DoctorWkt/MMU09/um6809/6809.c

/*
    6809.c   	-	cycle accurate simple 6809 cpu emulator
    Copyright (C) 2001  Arto Salmi
                        Joze Fabcic

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
    You should have received a copy of the GNU General Public License
    along with this program; if not, write to the Free Software
    Foundation, Inc., 675 Mass Ave, Cambridge, MA 02139, USA.
*/


#include "6809.h"

unsigned X, Y, S, U, PC;
unsigned A, B, DP;
unsigned H, N, Z, V, C;
unsigned EFI;

unsigned iPC;

UINT8 *memory = NULL;

unsigned ea = 0;
int cpu_clk = 0;
int cpu_period = 0;
int cpu_quit = 1;

unsigned *index_regs[4] = { &X, &Y, &U, &S };

unsigned imm_byte (void)
{
  unsigned val = memory[PC & 0xffff]; PC++;
  return val;
}

unsigned imm_word (void)
{
  unsigned val = (memory[PC & 0xffff] << 8) | memory[(PC + 1) & 0xffff]; PC += 2; 
  return val;
}

static void WRMEM (unsigned addr, unsigned data)
{
  memory[addr] = (UINT8)data;
}

void WRMEM16 (unsigned addr, unsigned data)
{
  WRMEM(addr,data >> 8);
  cpu_clk--;
  WRMEM((addr + 1) & 0xffff,data & 0xff);
}

unsigned RDMEM (unsigned addr)
{
  return memory[addr];
}

unsigned RDMEM16 (unsigned addr)
{
  unsigned val = RDMEM(addr) << 8;
  cpu_clk--;
  val |= RDMEM((addr + 1) & 0xffff);
  return val;
}

#define write_stack WRMEM
#define read_stack  RDMEM

void write_stack16 (unsigned addr, unsigned data)
{
  write_stack((addr + 1) & 0xffff,data & 0xff); 
  write_stack(addr,data >> 8);
}

unsigned read_stack16 (unsigned addr)
{
  return (read_stack(addr) << 8) | read_stack((addr + 1) & 0xffff);
}

void direct (void)
{
  unsigned val = memory[PC & 0xffff] | DP; PC++;
  ea = val;
}

void indexed (void) /* note take 1 extra cycle */
{
   unsigned post = imm_byte();
   unsigned *R   = index_regs[(post >> 5) & 0x3];
 
   if (post & 0x80)
   {
     switch (post & 0x1f)
     {
       case 0x00: ea = *R; *R = (*R + 1) & 0xffff;                  cpu_clk -= 6; break;
       case 0x01: ea = *R; *R = (*R + 2) & 0xffff;                  cpu_clk -= 7; break;
       case 0x02: *R = (*R - 1) & 0xffff; ea = *R;                  cpu_clk -= 6; break;
       case 0x03: *R = (*R - 2) & 0xffff; ea = *R;                  cpu_clk -= 7; break;
       case 0x04: ea = *R;                                          cpu_clk -= 4; break;
       case 0x05: ea = (*R + ((INT8)B)) & 0xffff;                   cpu_clk -= 5; break;
       case 0x06: ea = (*R + ((INT8)A)) & 0xffff;                   cpu_clk -= 5; break;
       case 0x08: ea = (*R + ((INT8)imm_byte())) & 0xffff;          cpu_clk -= 5; break;
       case 0x09: ea = (*R + imm_word()) & 0xffff;                  cpu_clk -= 8; break;
       case 0x0b: ea = (*R + get_d()) & 0xffff;                     cpu_clk -= 8; break;
       case 0x0c: ea = (INT8)imm_byte(); ea = (ea + PC) & 0xffff;   cpu_clk -= 5; break; 
       case 0x0d: ea = imm_word(); ea = (ea + PC) & 0xffff;         cpu_clk -= 9; break;

       case 0x11: ea = *R; *R = (*R + 2) & 0xffff;                  cpu_clk -= 7; ea = RDMEM16(ea); cpu_clk -= 2; break;
       case 0x13: *R = (*R - 2) & 0xffff; ea = *R;                  cpu_clk -= 7; ea = RDMEM16(ea); cpu_clk -= 2; break;
       case 0x14: ea = *R;                                          cpu_clk -= 4; ea = RDMEM16(ea); cpu_clk -= 2; break;
       case 0x15: ea = (*R + ((INT8)B)) & 0xffff;                   cpu_clk -= 5; ea = RDMEM16(ea); cpu_clk -= 2; break;
       case 0x16: ea = (*R + ((INT8)A)) & 0xffff;                   cpu_clk -= 5; ea = RDMEM16(ea); cpu_clk -= 2; break;
       case 0x18: ea = (*R + ((INT8)imm_byte())) & 0xffff;          cpu_clk -= 5; ea = RDMEM16(ea); cpu_clk -= 2; break;
       case 0x19: ea = (*R + imm_word()) & 0xffff;                  cpu_clk -= 8; ea = RDMEM16(ea); cpu_clk -= 2; break;
       case 0x1b: ea = (*R + get_d()) & 0xffff;                     cpu_clk -= 8; ea = RDMEM16(ea); cpu_clk -= 2; break;
       case 0x1c: ea = (INT8)imm_byte(); ea = (ea + PC) & 0xffff;   cpu_clk -= 5; ea = RDMEM16(ea); cpu_clk -= 2; break;
       case 0x1d: ea = imm_word(); ea = (ea + PC) & 0xffff;         cpu_clk -= 9; ea = RDMEM16(ea); cpu_clk -= 2; break;
       case 0x1f: ea = imm_word();                                  cpu_clk -= 6; ea = RDMEM16(ea); cpu_clk -= 2; break;      
       default:   ea = 0;  printf("%X: invalid index post $%02X\n",iPC,post); monitor_on = 1;                     break;
     }
   }
   else
   {
     if( post & 0x10) post |= 0xfff0; else post &= 0x000f;
     ea = (*R + post) & 0xffff;
     cpu_clk -= 5;
   }
}

void extended (void)
{
  unsigned val = (memory[PC & 0xffff] << 8) | memory[(PC + 1) & 0xffff]; PC += 2; 
  ea = val;
}

/* external register functions */

unsigned get_a  (void) { return A; }
unsigned get_b  (void) { return B; } 
unsigned get_dp (void) { return DP >> 8; }
unsigned get_x  (void) { return X; }
unsigned get_y  (void) { return Y; }
unsigned get_s  (void) { return S; }
unsigned get_u  (void) { return U; }
unsigned get_pc (void) { return PC & 0xffff; }
unsigned get_d  (void) { return (A<<8)|B; }

void set_a  (unsigned val) { A = val & 0xff; }
void set_b  (unsigned val) { B = val & 0xff; }
void set_dp (unsigned val) { DP = (val & 0xff) << 8; }
void set_x  (unsigned val) { X = val & 0xffff; }
void set_y  (unsigned val) { Y = val & 0xffff; }
void set_s  (unsigned val) { S = val & 0xffff; }
void set_u  (unsigned val) { U = val & 0xffff; }
void set_pc (unsigned val) { PC = val & 0xffff; }
void set_d  (unsigned val) { A = (val >> 8) & 0xff; B = val & 0xff; }

/* handle condition code register */

unsigned get_cc (void)
{
  unsigned res = EFI & (E_FLAG|F_FLAG|I_FLAG);

  if(H & 0x10) res |= H_FLAG;
  if(N & 0x80) res |= N_FLAG;
  if(Z == 0)   res |= Z_FLAG;
  if(V & 0x80) res |= V_FLAG;
  if(C != 0)   res |= C_FLAG;

  return res;
}

void set_cc (unsigned arg)
{
  EFI =   arg & (E_FLAG|F_FLAG|I_FLAG);
  H   =  (arg & H_FLAG ? 0x10 : 0);
  N   =  (arg & N_FLAG ? 0x80 : 0);
  Z   = (~arg)& Z_FLAG;
  V   =  (arg & V_FLAG ? 0x80 : 0);
  C   =   arg & C_FLAG; 
}

unsigned get_reg (unsigned nro)
{
  unsigned val = 0xff;

  switch (nro)
  {
    case  0: val = (A << 8) | B; break;
    case  1: val = X;            break;
    case  2: val = Y;            break;
    case  3: val = U;            break;
    case  4: val = S;            break;
    case  5: val = PC & 0xffff;  break;
    case  8: val = A;            break;
    case  9: val = B;            break;
    case 10: val = get_cc();     break;
    case 11: val = DP >> 8;      break;
  }

  return val;
}

void set_reg (unsigned nro, unsigned val)
{
  switch (nro)
  {
    case  0: A = val >> 8;
             B = val & 0xff; break;
    case  1: X = val;        break;
    case  2: Y = val;        break;
    case  3: U = val;        break;
    case  4: S = val;        break;
    case  5: PC = val;       break;
    case  8: A = val;        break;
    case  9: B = val;        break;
    case 10: set_cc(val);    break;
    case 11: DP = val << 8;  break;
  }
}

/* 8-Bit Accumulator and Memory Instructions */

unsigned adc (unsigned arg, unsigned val)
{
  unsigned res = arg + val + (C != 0);

  C = (res >> 1) & 0x80;
  N = Z = res &= 0xff;
  V = H = arg ^ val ^ res ^ C;
  
  return res;
}

unsigned add (unsigned arg, unsigned val)
{
  unsigned res = arg + val;

  C = (res >> 1) & 0x80;
  N = Z = res &= 0xff;
  V = H = arg ^ val ^ res ^ C;
 
  return res;
}

unsigned and (unsigned arg, unsigned val)
{
  unsigned res = arg & val;

  N = Z = res;
  V = 0;

  return res;
}

unsigned asl (unsigned arg) /* same as lsl */
{
  unsigned res = arg << 1;

  C = res & 0x100;
  N = Z = res &= 0xff;
  V = arg ^ res;
  cpu_clk -= 2;

  return res;
}

unsigned asr (unsigned arg)
{
  unsigned res = (INT8)arg;

  C = res & 1;
  N = Z = res = (res >> 1) & 0xff;
  cpu_clk -= 2;

  return res;
}

void bit (unsigned arg, unsigned val)
{
  unsigned res = arg & val;

  N = Z = res;
  V = 0;
}

unsigned clr (unsigned arg)
{
  C = N = Z = V = arg = 0;
  cpu_clk -= 2;

  return arg;
}

void cmp (unsigned arg, unsigned val)
{
  unsigned res = arg - val;

  C = res & 0x100;
  N = Z = res &= 0xff;
  V = (arg ^ val) & (arg ^ res);
}

unsigned com (unsigned arg)
{
  unsigned res = arg ^ 0xff;

  N = Z = res;
  V = 0; C = 1;
  cpu_clk -= 2;

  return res;
}

void daa (void)
{
  unsigned res = A;
  unsigned msn = res & 0xf0;
  unsigned lsn = res & 0x0f;

  if( lsn>0x09 || (H & 0x10)) res += 0x06;
  if( msn>0x80 &&   lsn>0x09) res += 0x60;
  if( msn>0x90 ||   (C != 0)) res += 0x60;

  C |= (res & 0x100);
  A = N = Z = res &= 0xff;
  V = 0; /* fix this */

  cpu_clk -= 2;
}

unsigned dec (unsigned arg)
{
  unsigned res = (arg - 1) & 0xff;

  N = Z = res;
  V = arg & ~res;
  cpu_clk -= 2;

  return res;
}

unsigned eor (unsigned arg, unsigned val)
{
  unsigned res = arg ^ val;

  N = Z = res;
  V = 0;

  return res;
}

void exg (void)
{
  unsigned tmp1 = 0xff;
  unsigned tmp2 = 0xff;
  unsigned post = imm_byte();

  if(((post ^ (post << 4)) & 0x80) == 0)
  {
    tmp1 = get_reg(post >> 4);
    tmp2 = get_reg(post & 15);
  }

  set_reg(post & 15, tmp1);
  set_reg(post >> 4, tmp2);

  cpu_clk -= 8;
}

unsigned inc (unsigned arg)
{
  unsigned res = (arg + 1) & 0xff;

  N = Z = res;
  V = ~arg & res;
  cpu_clk -= 2;

  return res;
}

unsigned ld (unsigned arg)
{
  unsigned res = arg;

  N = Z = res;
  V = 0;

  return res;
}

unsigned lsr (unsigned arg)
{
  unsigned res = arg >> 1;
 
  N = 0;
  Z = res;
  C = arg & 1;
  cpu_clk -= 2;

  return res;
}

void mul (void)
{
  unsigned res = (A * B) & 0xffff;

  Z = res;
  C = res & 0x80;
  A = res >> 8;
  B = res & 0xff;
  cpu_clk -= 11; 
}

unsigned neg (int arg)
{
  unsigned res = (-arg) & 0xff;

  C = N = Z = res;
  V = res & arg;
  cpu_clk -= 2;

  return res;
}

unsigned or (unsigned arg, unsigned val)
{
  unsigned res = arg | val;

  N = Z = res;
  V = 0;

  return res;
}

unsigned rol (unsigned arg)
{
  unsigned res = (arg << 1) + (C != 0);

  C = res & 0x100;
  N = Z = res &= 0xff;
  V = arg ^ res;
  cpu_clk -= 2;

  return res;
}

unsigned ror (unsigned arg)
{
  unsigned res = arg;

  if(C != 0) res |= 0x100;
  C = res & 1;
  N = Z = res >>= 1;
  cpu_clk -= 2;

  return res;
}

unsigned sbc (unsigned arg, unsigned val)
{
  unsigned res = arg - val - (C != 0);

  C = res & 0x100;
  N = Z = res &= 0xff;
  V = (arg ^ val) & (arg ^ res);

  return res;
}

void st (unsigned arg)
{
  unsigned res = arg;

  N = Z = res;
  V = 0;
  
  WRMEM(ea,res);
}

unsigned sub (unsigned arg, unsigned val)
{
  unsigned res = arg - val;

  C = res & 0x100;
  N = Z = res &= 0xff;
  V = (arg ^ val) & (arg ^ res);

  return res;
}

void tst (unsigned arg)
{
  unsigned res = arg;

  N = Z = res;
  V = 0;
  cpu_clk -= 2;
}

void tfr (void)
{
  unsigned tmp1 = 0xff;
  unsigned post = imm_byte();

  if(((post ^ (post << 4)) & 0x80) == 0) tmp1 = get_reg(post >> 4);

  set_reg(post & 15, tmp1);

  cpu_clk -= 6;
}


/* 16-Bit Accumulator Instructions */

void abx (void)
{
  X = (X + B) & 0xffff;
  cpu_clk -= 3;
}

void addd (unsigned val)
{
  unsigned arg = (A << 8) | B;
  unsigned res = arg + val;

  C = res & 0x10000;
  Z = res &= 0xffff;
  V = ((arg^res) & (val^res)) >> 8;
  A = N = res >> 8;
  B = res & 0xff;
}

void cmp16 (unsigned arg, unsigned val)
{
  unsigned res = arg - val;

  C = res & 0x10000;
  Z = res &= 0xffff;
  N = res >> 8;
  V = ((arg ^ val) & (arg ^ res)) >> 8;
}

void ldd (unsigned arg)
{
  unsigned res = arg;

  Z = res;
  A = N = res >> 8;
  B = res & 0xff;
  V = 0;
}

unsigned ld16 (unsigned arg)
{
  unsigned res = arg;

  Z = res;
  N = res >> 8;
  V = 0;

  return res;
}

void sex (void)
{
  unsigned res = B;

  Z = res;
  N = res &= 0x80;
  if(res != 0) res = 0xff;
  A = res;
  cpu_clk -= 2;
}

void std (void)
{
  unsigned res = (A << 8) | B;

  Z = res;
  N = A;
  V = 0;
  WRMEM16(ea,res);
}

void st16 (unsigned arg)
{
  unsigned res = arg;

  Z = res;
  N = res >> 8;
  V = 0;
  WRMEM16(ea,res);
}

void subd (unsigned val)
{
  unsigned arg = (A << 8) | B;
  unsigned res = arg - val;

  C = res & 0x10000;
  Z = res &= 0xffff;
  V = ((arg ^ val) & (arg ^ res)) >> 8;
  A = N = res >> 8;
  B = res & 0xff;
}

/* stack instructions */

void pshs (void)
{
  unsigned post = imm_byte();

  cpu_clk -= 5;
  
  if(post & 0x80) { cpu_clk -= 2; S = (S - 2) & 0xffff; write_stack16(S, PC & 0xffff); }
  if(post & 0x40) { cpu_clk -= 2; S = (S - 2) & 0xffff; write_stack16(S, U);      }
  if(post & 0x20) { cpu_clk -= 2; S = (S - 2) & 0xffff; write_stack16(S,  Y);     }
  if(post & 0x10) { cpu_clk -= 2; S = (S - 2) & 0xffff; write_stack16(S,  X);     }
  if(post & 0x08) { cpu_clk -= 1; S = (S - 1) & 0xffff; write_stack(S, DP >> 8);  }
  if(post & 0x04) { cpu_clk -= 1; S = (S - 1) & 0xffff; write_stack(S, B);        }
  if(post & 0x02) { cpu_clk -= 1; S = (S - 1) & 0xffff; write_stack(S, A);        }
  if(post & 0x01) { cpu_clk -= 1; S = (S - 1) & 0xffff; write_stack(S, get_cc()); } 
}

void pshu (void)
{
  unsigned post = imm_byte();

  cpu_clk -= 5;

  if(post & 0x80) { cpu_clk -= 2; U = (U - 2) & 0xffff; write_stack16(U, PC & 0xffff); }
  if(post & 0x40) { cpu_clk -= 2; U = (U - 2) & 0xffff; write_stack16(U, S);      }
  if(post & 0x20) { cpu_clk -= 2; U = (U - 2) & 0xffff; write_stack16(U,  Y);     }
  if(post & 0x10) { cpu_clk -= 2; U = (U - 2) & 0xffff; write_stack16(U,  X);     }
  if(post & 0x08) { cpu_clk -= 1; U = (U - 1) & 0xffff; write_stack(U, DP >> 8);  }
  if(post & 0x04) { cpu_clk -= 1; U = (U - 1) & 0xffff; write_stack(U, B);        }
  if(post & 0x02) { cpu_clk -= 1; U = (U - 1) & 0xffff; write_stack(U, A);        }
  if(post & 0x01) { cpu_clk -= 1; U = (U - 1) & 0xffff; write_stack(U, get_cc()); } 
}

void puls (void)
{
  unsigned post = imm_byte();

  cpu_clk -= 5;

  if(post & 0x01) { cpu_clk -= 1; set_cc(read_stack(S));     S = (S + 1) & 0xffff; }
  if(post & 0x02) { cpu_clk -= 1; A   = read_stack(S);       S = (S + 1) & 0xffff; }
  if(post & 0x04) { cpu_clk -= 1; B   = read_stack(S);       S = (S + 1) & 0xffff; }
  if(post & 0x08) { cpu_clk -= 1; DP  = read_stack(S) << 8;  S = (S + 1) & 0xffff; }
  if(post & 0x10) { cpu_clk -= 2; X   = read_stack16(S);     S = (S + 2) & 0xffff; }
  if(post & 0x20) { cpu_clk -= 2; Y   = read_stack16(S);     S = (S + 2) & 0xffff; }
  if(post & 0x40) { cpu_clk -= 2; U   = read_stack16(S);     S = (S + 2) & 0xffff; }
  if(post & 0x80) { cpu_clk -= 2; PC  = read_stack16(S);     S = (S + 2) & 0xffff; }
}

void pulu (void)
{
  unsigned post = imm_byte();

  cpu_clk -= 5;

  if(post & 0x01) { cpu_clk -= 1; set_cc(read_stack(U));     U = (U + 1) & 0xffff; }
  if(post & 0x02) { cpu_clk -= 1; A   = read_stack(U);       U = (U + 1) & 0xffff; }
  if(post & 0x04) { cpu_clk -= 1; B   = read_stack(U);       U = (U + 1) & 0xffff; }
  if(post & 0x08) { cpu_clk -= 1; DP  = read_stack(U) << 8;  U = (U + 1) & 0xffff; }
  if(post & 0x10) { cpu_clk -= 2; X   = read_stack16(U);     U = (U + 2) & 0xffff; }
  if(post & 0x20) { cpu_clk -= 2; Y   = read_stack16(U);     U = (U + 2) & 0xffff; }
  if(post & 0x40) { cpu_clk -= 2; S   = read_stack16(U);     U = (U + 2) & 0xffff; }
  if(post & 0x80) { cpu_clk -= 2; PC  = read_stack16(U);     U = (U + 2) & 0xffff; }
}

/* Miscellaneous Instructions */

void nop (void)
{
  cpu_clk -= 2;
}

void jsr (void)
{
  S = (S - 2) & 0xffff; write_stack16(S, PC & 0xffff);     
  PC = ea;
}

void rti (void)
{
  cpu_clk -= 6;
  set_cc(read_stack(S));  S = (S + 1) & 0xffff;

  if((EFI & E_FLAG) != 0)
  {
    cpu_clk -= 9;
    A   = read_stack(S);       S = (S + 1) & 0xffff;
    B   = read_stack(S);       S = (S + 1) & 0xffff;
    DP  = read_stack(S) << 8;  S = (S + 1) & 0xffff;
    X   = read_stack16(S);     S = (S + 2) & 0xffff;
    Y   = read_stack16(S);     S = (S + 2) & 0xffff;
    U   = read_stack16(S);     S = (S + 2) & 0xffff;
  }
  PC  = read_stack16(S);     S = (S + 2) & 0xffff;
}

void rts (void)
{
  cpu_clk -= 5;
  PC  = read_stack16(S);     S = (S + 2) & 0xffff;
}

void swi (void)
{
  cpu_clk -= 19;
  EFI |= E_FLAG;
  S = (S - 2) & 0xffff; write_stack16(S, PC & 0xffff);
  S = (S - 2) & 0xffff; write_stack16(S, U);
  S = (S - 2) & 0xffff; write_stack16(S,  Y);
  S = (S - 2) & 0xffff; write_stack16(S,  X);
  S = (S - 1) & 0xffff; write_stack(S, DP >> 8);
  S = (S - 1) & 0xffff; write_stack(S, B);
  S = (S - 1) & 0xffff; write_stack(S, A);
  S = (S - 1) & 0xffff; write_stack(S, get_cc());
  EFI |= (I_FLAG|F_FLAG);

  PC = (memory[0xfffa] << 8) | memory[0xfffb];
}

void swi3 (void)
{
  cpu_clk -= 20;
  EFI |= E_FLAG;
  S = (S - 2) & 0xffff; write_stack16(S, PC & 0xffff);
  S = (S - 2) & 0xffff; write_stack16(S, U);
  S = (S - 2) & 0xffff; write_stack16(S,  Y);
  S = (S - 2) & 0xffff; write_stack16(S,  X);
  S = (S - 1) & 0xffff; write_stack(S, DP >> 8);
  S = (S - 1) & 0xffff; write_stack(S, B);
  S = (S - 1) & 0xffff; write_stack(S, A);
  S = (S - 1) & 0xffff; write_stack(S, get_cc());

  PC = (memory[0xfff2] << 8) | memory[0xfff3];
}

void cwai (void)
{
  puts("CWAI - not suported yet!");
}

void sync (void)
{
  // puts("SYNC - not suported yet!");
  // cpu_clk -= 4;
  exit(0);
}

void orcc (void)
{
  unsigned tmp = imm_byte();

  set_cc( get_cc() | tmp);
  cpu_clk -= 3;
}

void andcc (void)
{
  unsigned tmp = imm_byte();

  set_cc( get_cc() & tmp);
  cpu_clk -= 3;
}

/* Branch Instructions */

#define cond_HI() ((Z != 0) && (C == 0))
#define cond_LS() ((Z == 0) || (C != 0))
#define cond_HS() (C == 0)
#define cond_LO() (C != 0)
#define cond_NE() (Z != 0)
#define cond_EQ() (Z == 0)
#define cond_VC() ((V & 0x80) == 0)
#define cond_VS() ((V & 0x80) != 0)
#define cond_PL() ((N & 0x80) == 0)
#define cond_MI() ((N & 0x80) != 0)
#define cond_GE() (((N^V) & 0x80) == 0)
#define cond_LT() (((N^V) & 0x80) != 0)
#define cond_GT() ((((N^V) & 0x80) == 0) && (Z != 0))
#define cond_LE() ((((N^V) & 0x80) != 0) || (Z == 0))

void bra (void)
{
  INT8 tmp = (INT8)imm_byte();
  PC += tmp;
}

void branch (unsigned cond)
{
  if (cond) bra();
  else PC++;

  cpu_clk -= 3;
}

void long_bra (void)
{
  INT16 tmp = (INT16)imm_word();
  PC += tmp;
}

void long_branch (unsigned cond)
{
  if (cond)
  {
    long_bra();
    cpu_clk -= 6;
  }
  else
  {
    PC += 2;
    cpu_clk -= 5;
  }
}

void long_bsr (void)
{
  INT16 tmp = (INT16)imm_word();
  ea = PC + tmp;
  S = (S - 2) & 0xffff; write_stack16(S, PC & 0xffff);     
  PC = ea;
  cpu_clk -= 9;
}

void bsr (void)
{
  INT8 tmp = (INT8)imm_byte();
  ea = PC + tmp;
  S = (S - 2) & 0xffff; write_stack16(S, PC & 0xffff);     
  PC = ea;
  cpu_clk -= 7;
}

/* execute 6809 code */

int cpu_execute (int cycles)
{
  unsigned opcode;

  cpu_period = cpu_clk = cycles;

  do
  {
    if (check_break(PC) != 0) monitor_on = 1;
    if (monitor_on != 0) if (monitor6809() != 0) return cpu_period - cpu_clk;

    iPC = PC;
    opcode = imm_byte();

    switch (opcode)
    {
      case 0x00: direct();   cpu_clk -= 4; WRMEM(ea, neg(RDMEM(ea))); break; /* NEG direct */
      case 0x03: direct();   cpu_clk -= 4; WRMEM(ea, com(RDMEM(ea))); break; /* COM direct */
      case 0x04: direct();   cpu_clk -= 4; WRMEM(ea, lsr(RDMEM(ea))); break; /* LSR direct */
      case 0x06: direct();   cpu_clk -= 4; WRMEM(ea, ror(RDMEM(ea))); break; /* ROR direct */
      case 0x07: direct();   cpu_clk -= 4; WRMEM(ea, asr(RDMEM(ea))); break; /* ASR direct */
      case 0x08: direct();   cpu_clk -= 4; WRMEM(ea, asl(RDMEM(ea))); break; /* ASL direct */
      case 0x09: direct();   cpu_clk -= 4; WRMEM(ea, rol(RDMEM(ea))); break; /* ROL direct */
      case 0x0a: direct();   cpu_clk -= 4; WRMEM(ea, dec(RDMEM(ea))); break; /* DEC direct */
      case 0x0c: direct();   cpu_clk -= 4; WRMEM(ea, inc(RDMEM(ea))); break; /* INC direct */
      case 0x0d: direct();   cpu_clk -= 4;           tst(RDMEM(ea));  break; /* TST direct */
      case 0x0e: direct();   cpu_clk -= 3;           PC = ea;         break; /* JMP direct */
      case 0x0f: direct();   cpu_clk -= 4; WRMEM(ea, clr(RDMEM(ea))); break; /* CLR direct */

      case 0x10:
      {
        opcode = imm_byte();

        switch (opcode)
        {
          case 0x21:                        cpu_clk -= 5; PC += 2;                               break;
          case 0x22:                                      long_branch( cond_HI() );              break;
          case 0x23:                                      long_branch( cond_LS() );              break;
          case 0x24:                                      long_branch( cond_HS() );              break;
          case 0x25:                                      long_branch( cond_LO() );              break;
          case 0x26:                                      long_branch( cond_NE() );              break;
          case 0x27:                                      long_branch( cond_EQ() );              break;
          case 0x28:                                      long_branch( cond_VC() );              break;
          case 0x29:                                      long_branch( cond_VS() );              break;
          case 0x2a:                                      long_branch( cond_PL() );              break;
          case 0x2b:                                      long_branch( cond_MI() );              break;
          case 0x2c:                                      long_branch( cond_GE() );              break;
          case 0x2d:                                      long_branch( cond_LT() );              break;
          case 0x2e:                                      long_branch( cond_GT() );              break;
          case 0x2f:                                      long_branch( cond_LE() );              break;
          case 0x3f:                                      swi2();                                break;
          case 0x83:                        cpu_clk -= 5; cmp16(get_d(),imm_word());             break;
          case 0x8c:                        cpu_clk -= 5; cmp16(Y,imm_word());                   break;
          case 0x8e:                        cpu_clk -= 4; Y = ld16(imm_word());                  break;
          case 0x93:            direct();   cpu_clk -= 5; cmp16(get_d(),RDMEM16(ea)); cpu_clk--; break;
          case 0x9c:            direct();   cpu_clk -= 5; cmp16(Y, RDMEM16(ea));      cpu_clk--; break;
          case 0x9e:            direct();   cpu_clk -= 5; Y = ld16(RDMEM16(ea));                 break;
          case 0x9f:            direct();   cpu_clk -= 5; st16(Y);                               break;
          case 0xa3: cpu_clk--; indexed();                cmp16(get_d(),RDMEM16(ea)); cpu_clk--; break;
          case 0xac: cpu_clk--; indexed();                cmp16(Y,RDMEM16(ea));       cpu_clk--; break;
          case 0xae: cpu_clk--; indexed();                Y = ld16(RDMEM16(ea));                 break;
          case 0xaf: cpu_clk--; indexed();                st16(Y); break;
          case 0xb3:            extended(); cpu_clk -= 6; cmp16(get_d(),RDMEM16(ea)); cpu_clk--; break;
          case 0xbc:            extended(); cpu_clk -= 6; cmp16(Y,RDMEM16(ea));       cpu_clk--; break;
          case 0xbe:            extended(); cpu_clk -= 6; Y = ld16(RDMEM16(ea));                 break;
          case 0xbf:            extended(); cpu_clk -= 6; st16(Y); break;
          case 0xce:                        cpu_clk -= 4; S = ld16(imm_word());                  break;
          case 0xde:            direct();   cpu_clk -= 5; S = ld16(RDMEM16(ea));                 break;
          case 0xdf:            direct();   cpu_clk -= 5; st16(S);                               break; 
          case 0xee: cpu_clk--; indexed();                S = ld16(RDMEM16(ea));                 break;
          case 0xef: cpu_clk--; indexed();                st16(S);                               break; 
          case 0xfe:            extended(); cpu_clk -= 6; S = ld16(RDMEM16(ea));                 break;
          case 0xff:            extended(); cpu_clk -= 6; st16(S);                               break;
          default:   printf("%X: invalid opcode $10%02X\n",iPC,opcode); monitor_on = 1;          break;
        }           
      }
      break;

      case 0x11:
      {
        opcode = imm_byte();

        switch (opcode)
        {
          case 0x3f:                                      swi3();                                break;
          case 0x83:                        cpu_clk -= 5; cmp16(U,imm_word());                   break;
          case 0x8c:                        cpu_clk -= 5; cmp16(S,imm_word());                   break;
          case 0x93:            direct();   cpu_clk -= 5; cmp16(U,RDMEM16(ea));       cpu_clk--; break;
          case 0x9c:            direct();   cpu_clk -= 5; cmp16(S,RDMEM16(ea));       cpu_clk--; break;
          case 0xa3: cpu_clk--; indexed();                cmp16(U,RDMEM16(ea));       cpu_clk--; break;
          case 0xac: cpu_clk--; indexed();                cmp16(S,RDMEM16(ea));       cpu_clk--; break;
          case 0xb3:            extended(); cpu_clk -= 6; cmp16(U,RDMEM16(ea));       cpu_clk--; break;
          case 0xbc:            extended(); cpu_clk -= 6; cmp16(S,RDMEM16(ea));       cpu_clk--; break;
          default:   printf("%X: invalid opcode $11%02X\n",iPC,opcode); monitor_on = 1;          break;
        }
      }
      break;

      case 0x12: nop();                    break;
      case 0x13: sync();                   break;
      case 0x16: long_bra(); cpu_clk -= 5; break;
      case 0x17: long_bsr();               break;
      case 0x19: daa();                    break;
      case 0x1a: orcc();                   break;
      case 0x1c: andcc();                  break;
      case 0x1d: sex();                    break;
      case 0x1e: exg();                    break;
      case 0x1f: tfr();                    break;

      case 0x20: bra();               cpu_clk -= 3; break;
      case 0x21: PC++;                cpu_clk -= 3; break;
      case 0x22: branch( cond_HI() );               break;
      case 0x23: branch( cond_LS() );               break;
      case 0x24: branch( cond_HS() );               break;
      case 0x25: branch( cond_LO() );               break;
      case 0x26: branch( cond_NE() );               break;
      case 0x27: branch( cond_EQ() );               break;
      case 0x28: branch( cond_VC() );               break;
      case 0x29: branch( cond_VS() );               break;
      case 0x2a: branch( cond_PL() );               break;
      case 0x2b: branch( cond_MI() );               break;
      case 0x2c: branch( cond_GE() );               break;
      case 0x2d: branch( cond_LT() );               break;
      case 0x2e: branch( cond_GT() );               break;
      case 0x2f: branch( cond_LE() );               break;

      case 0x30: indexed();                          Z = X = ea;      break; /* LEAX indexed */
      case 0x31: indexed();                          Z = Y = ea;      break; /* LEAY indexed */
      case 0x32: indexed();                          S = ea;          break; /* LEAS indexed */
      case 0x33: indexed();                          U = ea;          break; /* LEAU indexed */
      case 0x34:                                     pshs();          break; /* PSHS implied */
      case 0x35:                                     puls();          break; /* PULS implied */
      case 0x36:                                     pshu();          break; /* PSHU implied */
      case 0x37:                                     pulu();          break; /* PULU implied */
      case 0x39:                                     rts();           break; /* RTS implied  */
      case 0x3a:                                     abx();           break; /* ABX implied  */
      case 0x3b:                                     rti();           break; /* RTI implied  */
      case 0x3c:                                     cwai();          break; /* CWAI implied */
      case 0x3d:                                     mul();           break; /* MUL implied  */
      case 0x3f:                                     swi();           break; /* SWI implied  */

      case 0x40: A = neg(A); break; /* NEGA implied */
      case 0x43: A = com(A); break; /* COMA implied */
      case 0x44: A = lsr(A); break; /* LSRA implied */
      case 0x46: A = ror(A); break; /* RORA implied */
      case 0x47: A = asr(A); break; /* ASRA implied */
      case 0x48: A = asl(A); break; /* ASLA implied */
      case 0x49: A = rol(A); break; /* ROLA implied */
      case 0x4a: A = dec(A); break; /* DECA implied */
      case 0x4c: A = inc(A); break; /* INCA implied */
      case 0x4d:     tst(A); break; /* TSTA implied */
      case 0x4f: A = clr(A); break; /* CLRA implied */

      case 0x50: B = neg(B); break; /* NEGB implied */
      case 0x53: B = com(B); break; /* COMB implied */
      case 0x54: B = lsr(B); break; /* LSRB implied */
      case 0x56: B = ror(B); break; /* RORB implied */
      case 0x57: B = asr(B); break; /* ASRB implied */
      case 0x58: B = asl(B); break; /* ASLB implied */
      case 0x59: B = rol(B); break; /* ROLB implied */
      case 0x5a: B = dec(B); break; /* DECB implied */
      case 0x5c: B = inc(B); break; /* INCB implied */
      case 0x5d:     tst(B); break; /* TSTB implied */
      case 0x5f: B = clr(B); break; /* CLRB implied */

      case 0x60: indexed();                WRMEM(ea, neg(RDMEM(ea))); break; /* NEG indexed */
      case 0x63: indexed();                WRMEM(ea, com(RDMEM(ea))); break; /* COM indexed */
      case 0x64: indexed();                WRMEM(ea, lsr(RDMEM(ea))); break; /* LSR indexed */
      case 0x66: indexed();                WRMEM(ea, ror(RDMEM(ea))); break; /* ROR indexed */
      case 0x67: indexed();                WRMEM(ea, asr(RDMEM(ea))); break; /* ASR indexed */
      case 0x68: indexed();                WRMEM(ea, asl(RDMEM(ea))); break; /* ASL indexed */
      case 0x69: indexed();                WRMEM(ea, rol(RDMEM(ea))); break; /* ROL indexed */
      case 0x6a: indexed();                WRMEM(ea, dec(RDMEM(ea))); break; /* DEC indexed */
      case 0x6c: indexed();                WRMEM(ea, inc(RDMEM(ea))); break; /* INC indexed */
      case 0x6d: indexed();                          tst(RDMEM(ea));  break; /* TST indexed */
      case 0x6e: indexed();  cpu_clk += 1;           PC = ea;         break; /* JMP indexed */
      case 0x6f: indexed();                WRMEM(ea, clr(RDMEM(ea))); break; /* CLR indexed */

      case 0x70: extended(); cpu_clk -= 5; WRMEM(ea, neg(RDMEM(ea))); break; /* NEG extended */
      case 0x73: extended(); cpu_clk -= 5; WRMEM(ea, com(RDMEM(ea))); break; /* COM extended */
      case 0x74: extended(); cpu_clk -= 5; WRMEM(ea, lsr(RDMEM(ea))); break; /* LSR extended */
      case 0x76: extended(); cpu_clk -= 5; WRMEM(ea, ror(RDMEM(ea))); break; /* ROR extended */
      case 0x77: extended(); cpu_clk -= 5; WRMEM(ea, asr(RDMEM(ea))); break; /* ASR extended */
      case 0x78: extended(); cpu_clk -= 5; WRMEM(ea, asl(RDMEM(ea))); break; /* ASL extended */
      case 0x79: extended(); cpu_clk -= 5; WRMEM(ea, rol(RDMEM(ea))); break; /* ROL extended */
      case 0x7a: extended(); cpu_clk -= 5; WRMEM(ea, dec(RDMEM(ea))); break; /* DEC extended */
      case 0x7c: extended(); cpu_clk -= 5; WRMEM(ea, inc(RDMEM(ea))); break; /* INC extended */
      case 0x7d: extended(); cpu_clk -= 5;           tst(RDMEM(ea));  break; /* TST extended */
      case 0x7e: extended(); cpu_clk -= 4;           PC = ea;         break; /* JMP extended */
      case 0x7f: extended(); cpu_clk -= 5; WRMEM(ea, clr(RDMEM(ea))); break; /* CLR extended */

      case 0x80:             cpu_clk -= 2; A = sub(A, imm_byte());    break;
      case 0x81:             cpu_clk -= 2;     cmp(A, imm_byte());    break;
      case 0x82:             cpu_clk -= 2; A = sbc(A, imm_byte());    break;
      case 0x83:             cpu_clk -= 4;     subd(imm_word());      break;
      case 0x84:             cpu_clk -= 2; A = and(A, imm_byte());    break;
      case 0x85:             cpu_clk -= 2;     bit(A, imm_byte());    break;
      case 0x86:             cpu_clk -= 2; A = ld(imm_byte());        break;
      case 0x88:             cpu_clk -= 2; A = eor(A, imm_byte());    break;
      case 0x89:             cpu_clk -= 2; A = adc(A, imm_byte());    break;
      case 0x8a:             cpu_clk -= 2; A = or(A, imm_byte());     break;
      case 0x8b:             cpu_clk -= 2; A = add(A, imm_byte());    break;
      case 0x8c:             cpu_clk -= 4;     cmp16(X, imm_word());  break;
      case 0x8d:                               bsr();                 break;
      case 0x8e:             cpu_clk -= 3; X = ld16(imm_word());      break;

      case 0x90: direct();   cpu_clk -= 4; A = sub(A, RDMEM(ea));     break;
      case 0x91: direct();   cpu_clk -= 4;     cmp(A, RDMEM(ea));     break;
      case 0x92: direct();   cpu_clk -= 4; A = sbc(A, RDMEM(ea));     break;
      case 0x93: direct();   cpu_clk -= 4;     subd(RDMEM16(ea));     cpu_clk--; break;
      case 0x94: direct();   cpu_clk -= 4; A = and(A, RDMEM(ea));     break;
      case 0x95: direct();   cpu_clk -= 4;     bit(A, RDMEM(ea));     break;
      case 0x96: direct();   cpu_clk -= 4; A = ld(RDMEM(ea));         break;
      case 0x97: direct();   cpu_clk -= 4;     st(A);                 break;
      case 0x98: direct();   cpu_clk -= 4; A = eor(A, RDMEM(ea));     break;
      case 0x99: direct();   cpu_clk -= 4; A = adc(A, RDMEM(ea));     break;
      case 0x9a: direct();   cpu_clk -= 4; A = or(A, RDMEM(ea));      break;
      case 0x9b: direct();   cpu_clk -= 4; A = add(A, RDMEM(ea));     break;
      case 0x9c: direct();   cpu_clk -= 4;     cmp16(X, RDMEM16(ea)); cpu_clk--; break;
      case 0x9d: direct();   cpu_clk -= 7; jsr();                     break;
      case 0x9e: direct();   cpu_clk -= 4; X = ld16(RDMEM16(ea));     break;
      case 0x9f: direct();   cpu_clk -= 4; st16(X);                   break;

      case 0xa0: indexed();                A = sub(A, RDMEM(ea));     break;
      case 0xa1: indexed();                cmp(A, RDMEM(ea));         break;
      case 0xa2: indexed();                A = sbc(A, RDMEM(ea));     break;
      case 0xa3: indexed();                subd(RDMEM16(ea));         cpu_clk--; break;
      case 0xa4: indexed();                A = and(A, RDMEM(ea));     break;
      case 0xa5: indexed();                bit(A, RDMEM(ea));         break;
      case 0xa6: indexed();                A = ld(RDMEM(ea));         break;
      case 0xa7: indexed();                st(A);                     break;
      case 0xa8: indexed();                A = eor(A, RDMEM(ea));     break;
      case 0xa9: indexed();                A = adc(A, RDMEM(ea));     break;
      case 0xaa: indexed();                A = or(A, RDMEM(ea));      break;
      case 0xab: indexed();                A = add(A, RDMEM(ea));     break;
      case 0xac: indexed();                cmp16(X, RDMEM16(ea));     cpu_clk--; break;
      case 0xad: indexed();  cpu_clk -= 3; jsr();                     break;
      case 0xae: indexed();                X = ld16(RDMEM16(ea));     break;
      case 0xaf: indexed();                st16(X);                   break;

      case 0xb0: extended(); cpu_clk -= 5; A = sub(A, RDMEM(ea));     break;
      case 0xb1: extended(); cpu_clk -= 5;     cmp(A, RDMEM(ea));     break;
      case 0xb2: extended(); cpu_clk -= 5; A = sbc(A, RDMEM(ea));     break;
      case 0xb3: extended(); cpu_clk -= 5;     subd(RDMEM16(ea));     cpu_clk--; break;
      case 0xb4: extended(); cpu_clk -= 5; A = and(A, RDMEM(ea));     break;
      case 0xb5: extended(); cpu_clk -= 5;     bit(A, RDMEM(ea));     break;
      case 0xb6: extended(); cpu_clk -= 5; A = ld(RDMEM(ea));         break;
      case 0xb7: extended(); cpu_clk -= 5;     st(A);                 break;
      case 0xb8: extended(); cpu_clk -= 5; A = eor(A, RDMEM(ea));     break;
      case 0xb9: extended(); cpu_clk -= 5; A = adc(A, RDMEM(ea));     break;
      case 0xba: extended(); cpu_clk -= 5; A = or(A, RDMEM(ea));      break;
      case 0xbb: extended(); cpu_clk -= 5; A = add(A, RDMEM(ea));     break;
      case 0xbc: extended(); cpu_clk -= 5;     cmp16(X, RDMEM16(ea)); cpu_clk--; break;
      case 0xbd: extended(); cpu_clk -= 8; jsr();                     break;
      case 0xbe: extended(); cpu_clk -= 5; X = ld16(RDMEM16(ea));     break;
      case 0xbf: extended(); cpu_clk -= 5; st16(X);                   break;

      case 0xc0:             cpu_clk -= 2; B = sub(B, imm_byte());    break;
      case 0xc1:             cpu_clk -= 2;     cmp(B, imm_byte());    break;
      case 0xc2:             cpu_clk -= 2; B = sbc(B, imm_byte());    break;
      case 0xc3:             cpu_clk -= 4;     addd(imm_word());      break;
      case 0xc4:             cpu_clk -= 2; B = and(B, imm_byte());    break;
      case 0xc5:             cpu_clk -= 2;     bit(B, imm_byte());    break;
      case 0xc6:             cpu_clk -= 2; B = ld(imm_byte());        break;
      case 0xc8:             cpu_clk -= 2; B = eor(B, imm_byte());    break;
      case 0xc9:             cpu_clk -= 2; B = adc(B, imm_byte());    break;
      case 0xca:             cpu_clk -= 2; B = or(B, imm_byte());     break;
      case 0xcb:             cpu_clk -= 2; B = add(B, imm_byte());    break;
      case 0xcc:             cpu_clk -= 3;     ldd(imm_word());       break;
      case 0xce:             cpu_clk -= 3; U = ld16(imm_word());      break;

      case 0xd0: direct();   cpu_clk -= 4; B = sub(B, RDMEM(ea));     break;
      case 0xd1: direct();   cpu_clk -= 4;     cmp(B, RDMEM(ea));     break;
      case 0xd2: direct();   cpu_clk -= 4; B = sbc(B, RDMEM(ea));     break;
      case 0xd3: direct();   cpu_clk -= 4;     addd(RDMEM16(ea));     cpu_clk--; break;
      case 0xd4: direct();   cpu_clk -= 4; B = and(B, RDMEM(ea));     break;
      case 0xd5: direct();   cpu_clk -= 4;     bit(B, RDMEM(ea));     break;
      case 0xd6: direct();   cpu_clk -= 4; B = ld(RDMEM(ea));         break;
      case 0xd7: direct();   cpu_clk -= 4;     st(B);                 break;
      case 0xd8: direct();   cpu_clk -= 4; B = eor(B, RDMEM(ea));     break;
      case 0xd9: direct();   cpu_clk -= 4; B = adc(B, RDMEM(ea));     break;
      case 0xda: direct();   cpu_clk -= 4; B = or(B, RDMEM(ea));      break;
      case 0xdb: direct();   cpu_clk -= 4; B = add(B, RDMEM(ea));     break;
      case 0xdc: direct();   cpu_clk -= 4;     ldd(RDMEM16(ea));      break;
      case 0xdd: direct();   cpu_clk -= 4;     std();                 break;
      case 0xde: direct();   cpu_clk -= 4; U = ld16(RDMEM16(ea));     break;
      case 0xdf: direct();   cpu_clk -= 4;     st16(U);               break;

      case 0xe0: indexed();                B = sub(B, RDMEM(ea));     break;
      case 0xe1: indexed();                cmp(B, RDMEM(ea));         break;
      case 0xe2: indexed();                B = sbc(B, RDMEM(ea));     break;
      case 0xe3: indexed();                addd(RDMEM16(ea));         cpu_clk--; break;
      case 0xe4: indexed();                B = and(B, RDMEM(ea));     break;
      case 0xe5: indexed();                bit(B, RDMEM(ea));         break;
      case 0xe6: indexed();                B = ld(RDMEM(ea));         break;
      case 0xe7: indexed();                st(B);                     break;
      case 0xe8: indexed();                B = eor(B, RDMEM(ea));     break;
      case 0xe9: indexed();                B = adc(B, RDMEM(ea));     break;
      case 0xea: indexed();                B = or(B, RDMEM(ea));      break;
      case 0xeb: indexed();                B = add(B, RDMEM(ea));     break;
      case 0xec: indexed();                ldd(RDMEM16(ea));          break;
      case 0xed: indexed();                std();                     break;
      case 0xee: indexed();                U = ld16(RDMEM16(ea));     break;
      case 0xef: indexed();                st16(U);                   break;

      case 0xf0: extended(); cpu_clk -= 5; B = sub(B, RDMEM(ea));     break;
      case 0xf1: extended(); cpu_clk -= 5;     cmp(B, RDMEM(ea));     break;
      case 0xf2: extended(); cpu_clk -= 5; B = sbc(B, RDMEM(ea));     break;
      case 0xf3: extended(); cpu_clk -= 5;     addd(RDMEM16(ea));     cpu_clk--; break;
      case 0xf4: extended(); cpu_clk -= 5; B = and(B, RDMEM(ea));     break;
      case 0xf5: extended(); cpu_clk -= 5;     bit(B, RDMEM(ea));     break;
      case 0xf6: extended(); cpu_clk -= 5; B = ld(RDMEM(ea));         break;
      case 0xf7: extended(); cpu_clk -= 5;     st(B);                 break;
      case 0xf8: extended(); cpu_clk -= 5; B = eor(B, RDMEM(ea));     break;
      case 0xf9: extended(); cpu_clk -= 5; B = adc(B, RDMEM(ea));     break;
      case 0xfa: extended(); cpu_clk -= 5; B = or(B, RDMEM(ea));      break;
      case 0xfb: extended(); cpu_clk -= 5; B = add(B, RDMEM(ea));     break;
      case 0xfc: extended(); cpu_clk -= 5; ldd(RDMEM16(ea));          break;
      case 0xfd: extended(); cpu_clk -= 5; std();                     break;
      case 0xfe: extended(); cpu_clk -= 5; U = ld16(RDMEM16(ea));     break;
      case 0xff: extended(); cpu_clk -= 5; st16(U);                   break;

	default:   printf("%04X: invalid opcode $%02X\n",iPC,opcode); cpu_clk -= 2; 
          monitor_on = 1;
          break;
    }

  } while (cpu_clk > 0);

  return cpu_period - cpu_clk;
}

void cpu_reset (void)
{
  X = Y = A = B = DP = 0;
  H = N = V = C = 0; Z = 1;
  EFI = F_FLAG|I_FLAG;
  U = S = 0xffff;

  PC = 0x100;
}
