DoctorWkt/MMU09/um6809/6809.h

/*
    6809.h   	-	header for monitor and simulator
    Copyright (C) 2001  Arto Salmi

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
    You should have received a copy of the GNU General Public License
    along with this program; if not, write to the Free Software
    Foundation, Inc., 675 Mass Ave, Cambridge, MA 02139, USA.
*/


#ifndef M6809_H
#define M6809_H

#include <stdio.h>
#include <stdlib.h>
#include <string.h>

typedef unsigned char UINT8;
typedef signed char INT8;

typedef unsigned short UINT16;
typedef signed short INT16;

typedef unsigned int UINT32;
typedef signed int INT32;

#define E_FLAG 0x80
#define F_FLAG 0x40
#define H_FLAG 0x20
#define I_FLAG 0x10
#define N_FLAG 0x08
#define Z_FLAG 0x04
#define V_FLAG 0x02
#define C_FLAG 0x01

/* 6809.c */
extern UINT8 *memory;

extern int cpu_quit;
extern int cpu_execute (int);
extern void cpu_reset (void);

extern unsigned get_a  (void);
extern unsigned get_b  (void);
extern unsigned get_cc (void);
extern unsigned get_dp (void);
extern unsigned get_x  (void);
extern unsigned get_y  (void);
extern unsigned get_s  (void);
extern unsigned get_u  (void);
extern unsigned get_pc (void);
extern unsigned get_d  (void);
extern void set_a  (unsigned);
extern void set_b  (unsigned);
extern void set_cc (unsigned);
extern void set_dp (unsigned);
extern void set_x  (unsigned);
extern void set_y  (unsigned);
extern void set_s  (unsigned);
extern void set_u  (unsigned);
extern void set_pc (unsigned);
extern void set_d  (unsigned);

/* monitor.c */
extern int monitor_on;
extern int do_break;
extern int check_break (unsigned);
extern void monitor_init (void); 
extern int monitor6809 (void);
extern int dasm (char *, int);
extern void add_breakpoint (int break_pc);

extern int load_hex (char *);
extern int load_s19 (char *);
extern int load_bin (char *,int);

// oscode.c
extern void swi2 (void);
extern void set_arglist(int argc, char **argv);

#endif /* M6809_H */
